jackpham-rgb/accessisound-esp32s3/hardware/v2/diagram/lipo_crop.png

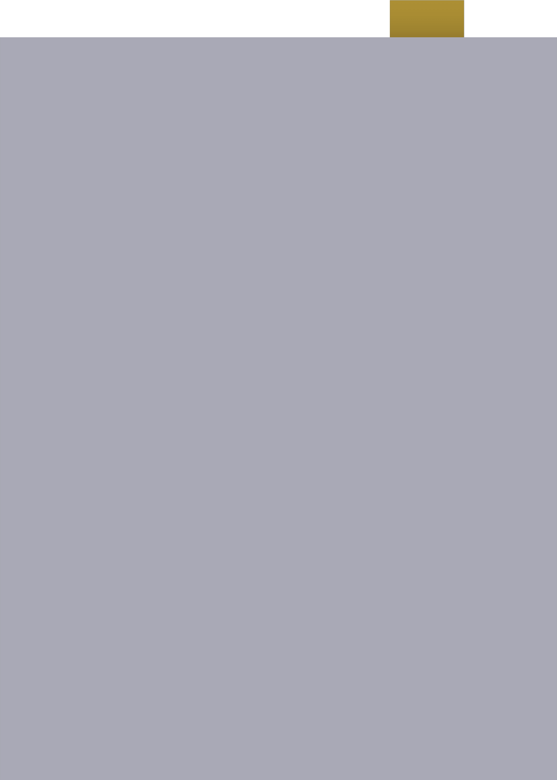
hardware/v2/diagram/lipo_crop.png
